4ms/SWN/src/lfo_wavetable_bank.c

// This file generated with wavecalc
// Authors: Hugo Paris, hugoplho@gmail.com, Dan Green danngreen1@gmail.com
//
// Wavetable name: 2018_08_05_HP_BetaTest_LFO_BANKS
// Wavetable by: Hugo Paris hugoplho@gmail.com

#include "arm_math.h"
#include "lfo_wavetable_bank.h"

const uint8_t lfo_sustain_pos[NUM_LFO_SHAPES] = {
	// RAMP(s) full, 3/4, 1/2,/ 18
	5,
	1,
	1,
	1,
	1,

	// REV RAMP full, 3/4, 1/2,/ 18
	243,
	192,
	128,
	64,
	32,

	// SINE, TRI, OFFSET
	133,
	134,
	128,

	// CPX SHAPES #1
	22,
	11,
	14,
	11,
	18,
	13,

	// CPX SHAPES #2
	9,
	11,
	11,
	23,
	11,
	41,
};

const uint8_t lfo_wavetable[NUM_LFO_SHAPES][LFO_TABLELEN] =
{
	// RAMP(s) full, 3/4, 1/2,/ 18

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
};
