4ms/SWN/src/sphere_flash_io.c

/*
 * sphere_flash_io.c - Spherical Wavetable Navigator I/O with external FLASH memory
 *
 * Author: Dan Green (danngreen1@gmail.com)
 *
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
 * See http://creativecommons.org/licenses/MIT/ for more information.
 *
 * -----------------------------------------------------------------------------
 */

#include "globals.h"
#include "sphere_flash_io.h"
#include "sphere.h"
#include "spheres_internal.h"

#include "drivers/flash_S25FL127.h"
#include "drivers/flashram_spidma.h"
#include "math_util.h"
#include "timekeeper.h"

#include "external_flash_layout.h"

const uint32_t 	WT_SIZE = sizeof(o_waveform)*WT_DIM_SIZE*WT_DIM_SIZE*WT_DIM_SIZE;


char	user_sphere_signature[4];
char	factory_sphere_signature[4];
char	cleared_user_sphere_signature[4];

enum SphereTypes sphere_types[MAX_TOTAL_SPHERES];

void init_sphere_flash(void)
{
	user_sphere_signature[0]='U';
	user_sphere_signature[1]='S';
	user_sphere_signature[2]='1';
	user_sphere_signature[3]='\0';

	factory_sphere_signature[0]='F';
	factory_sphere_signature[1]='S';
	factory_sphere_signature[2]='1';
	factory_sphere_signature[3]='\0';

	cleared_user_sphere_signature[0]='C';
	cleared_user_sphere_signature[1]='S';
	cleared_user_sphere_signature[2]='1';
	cleared_user_sphere_signature[3]='\0';
}

void write_factory_spheres_to_extflash(void)
{
#ifndef SKIP_FACTORY_SPHERES_IN_HEXFILE
	uint32_t wt_num;

	for (wt_num=0;wt_num<NUM_FACTORY_SPHERES;wt_num++) {
		save_sphere_to_flash(wt_num, SPHERE_TYPE_FACTORY, (int16_t *)wavetable_list[wt_num]);
	}
#endif
}
uint8_t is_wav_name(char *name) {
	uint32_t max_strlen = 31;
	uint8_t found = 0;
	while (!found && max_strlen--) {
		if (name[0]=='w' && name[1]=='a' && name[2]=='v')
			found = 1;
		if (name[0]=='s' && name[1]=='o' && name[2]=='p' && name[3]=='r')
			found = 1;
		name++;
	}
	return found;
}

void restore_factory_spheres_to_extflash(void)
{
#ifndef SKIP_FACTORY_SPHERES_IN_HEXFILE
	uint32_t wt_num;

	for (wt_num=0;wt_num<NUM_FACTORY_SPHERES;wt_num++) {
		if (read_spheretype(wt_num) != SPHERE_TYPE_FACTORY) {
			if (is_wav_name((char *)(wavetable_list[wt_num])))
				save_sphere_to_flash(wt_num, SPHERE_TYPE_FACTORY, (int16_t *)wavetable_list[wt_num]);
		}
	}
#endif
}

uint32_t get_wt_addr(uint16_t wt_num)
{
	if (wt_num >= MAX_TOTAL_SPHERES)
		wt_num = (MAX_TOTAL_SPHERES-1);

	return (sFLASH_get_sector_addr(WT_SECTOR_START + wt_num));
}	

// You must check if SPI DMA is busy before calling this or using *waveform.
// *waveform must point to a global or static memory space (not to the stack)
void load_extflash_wavetable(uint8_t wt_num, o_waveform *waveform, uint8_t x, uint8_t y, uint8_t z)
{
	uint32_t base_addr = get_wt_addr(wt_num);
	uint32_t addr;

	x = _CLAMP_U8(x,0,2);
	y = _CLAMP_U8(y,0,2);
	z = _CLAMP_U8(z,0,2);

	//calculate where the waveform is within the sphere
	addr = base_addr + sizeof(user_sphere_signature) + ((x + (y*WT_DIM_SIZE) + (z*WT_DIM_SIZE*WT_DIM_SIZE)) * SPHERE_WAVEFORM_SIZE);

	//sFLASH_read_buffer((uint8_t *)(waveform->name), addr, WT_NAME_MONITOR_CHARSIZE);

	addr += WT_NAME_MONITOR_CHARSIZE;

	sFLASH_read_buffer_DMA((uint8_t *)(waveform->wave), addr, WT_TABLELEN*BYTEDEPTH);
}

void load_extflash_wave_raw(uint8_t wt_num, int16_t *waveform, uint8_t x, uint8_t y, uint8_t z)
{
	uint32_t base_addr = get_wt_addr(wt_num);
	uint32_t addr;

	x = _CLAMP_U8(x,0,2);
	y = _CLAMP_U8(y,0,2);
	z = _CLAMP_U8(z,0,2);

	//calculate where the waveform is within the sphere
	addr = base_addr + sizeof(user_sphere_signature) + ((x + (y*WT_DIM_SIZE) + (z*WT_DIM_SIZE*WT_DIM_SIZE)) * SPHERE_WAVEFORM_SIZE);
	addr += WT_NAME_MONITOR_CHARSIZE;

	sFLASH_read_buffer_DMA((uint8_t *)waveform, addr, WT_TABLELEN*BYTEDEPTH);
}


void save_sphere_to_flash(uint8_t wt_num, enum SphereTypes sphere_type, int16_t *sphere_data){

	uint32_t sz;
	uint32_t base_addr = get_wt_addr(wt_num);

	pause_timer_IRQ(WT_INTERP_TIM_number);

	sFLASH_erase_sector(base_addr);

	//Write signature
	sz = 4;
	if (sphere_type == SPHERE_TYPE_USER)
		sFLASH_write_buffer((uint8_t *)user_sphere_signature, base_addr, sz);
	else
	if (sphere_type == SPHERE_TYPE_FACTORY)
		sFLASH_write_buffer((uint8_t *)factory_sphere_signature, base_addr, sz);
	else 
		return; //error, bad sphere_type

	base_addr += sz;

	sFLASH_write_buffer((uint8_t *)sphere_data, base_addr, WT_SIZE);

	resume_timer_IRQ(WT_INTERP_TIM_number);

	sphere_types[wt_num] = sphere_type;
}

void save_unformatted_sphere_to_flash(uint8_t wt_num, enum SphereTypes sphere_type, o_waveform sphere_data[WT_DIM_SIZE][WT_DIM_SIZE][WT_DIM_SIZE]){

	uint32_t sz;
	uint32_t base_addr = get_wt_addr(wt_num);
	uint8_t dim1 = 0;
	uint8_t dim2 = 0;
	uint8_t dim3 = 0;


	pause_timer_IRQ(WT_INTERP_TIM_number);

	sFLASH_erase_sector(base_addr);

	//Write signature
	sz = 4;
	if (sphere_type == SPHERE_TYPE_USER)
		sFLASH_write_buffer((uint8_t *)user_sphere_signature, base_addr, sz);
	else
	if (sphere_type == SPHERE_TYPE_FACTORY)
		sFLASH_write_buffer((uint8_t *)factory_sphere_signature, base_addr, sz);
	else 
		return; //error, bad sphere_type

	base_addr += sz;

	sz = sizeof(o_waveform);
	for (dim1=0; dim1<WT_DIM_SIZE; dim1++) {
		for (dim2=0; dim2<WT_DIM_SIZE; dim2++) {
			for (dim3=0; dim3<WT_DIM_SIZE; dim3++) {
				sFLASH_write_buffer((uint8_t *)(&sphere_data[dim3][dim2][dim1]), base_addr, sz);
				base_addr+=sz;
			}
		}
	}

	resume_timer_IRQ(WT_INTERP_TIM_number);

	sphere_types[wt_num] = sphere_type;
}

enum SphereTypes get_spheretype(uint32_t wt_num)
{
	return sphere_types[wt_num];
}

enum SphereTypes read_spheretype(uint32_t wt_num)
{
	uint32_t addr = get_wt_addr(wt_num);
	uint32_t sz;
	static char	read_sphere_type_data[4];

	pause_timer_IRQ(WT_INTERP_TIM_number);

	sz = 4;
	sFLASH_read_buffer((uint8_t *)read_sphere_type_data, addr, sz);

	resume_timer_IRQ(WT_INTERP_TIM_number);

	if (   read_sphere_type_data[0] == user_sphere_signature[0] 
		&& read_sphere_type_data[1] == user_sphere_signature[1] 
		&& read_sphere_type_data[2] == user_sphere_signature[2] 
		&& read_sphere_type_data[3] == user_sphere_signature[3] )
		return SPHERE_TYPE_USER;
	else
	if (   read_sphere_type_data[0] == factory_sphere_signature[0] 
		&& read_sphere_type_data[1] == factory_sphere_signature[1] 
		&& read_sphere_type_data[2] == factory_sphere_signature[2] 
		&& read_sphere_type_data[3] == factory_sphere_signature[3] )
		return SPHERE_TYPE_FACTORY;
	else
	if (   read_sphere_type_data[0] == cleared_user_sphere_signature[0] 
		&& read_sphere_type_data[1] == cleared_user_sphere_signature[1] 
		&& read_sphere_type_data[2] == cleared_user_sphere_signature[2] 
		&& read_sphere_type_data[3] == cleared_user_sphere_signature[3] )
		return SPHERE_TYPE_CLEARED;
	else
		return SPHERE_TYPE_EMPTY;

}

enum SphereTypes clear_user_sphere(uint8_t wt_num)
{
	uint32_t addr;
	uint32_t sz;
	static char	read_data[4];

	pause_timer_IRQ(WT_INTERP_TIM_number);

	sz = 4;
	addr = get_wt_addr(wt_num);
	sFLASH_read_buffer((uint8_t *)read_data, addr, sz);

	if ((sphere_types[wt_num]==SPHERE_TYPE_USER) ||
		(read_data[0] == user_sphere_signature[0] && read_data[1] == user_sphere_signature[1] && read_data[2] == user_sphere_signature[2] && read_data[3] == user_sphere_signature[3]))
	{
		sFLASH_write_buffer((uint8_t *)cleared_user_sphere_signature, addr, sz);
		sphere_types[wt_num] = SPHERE_TYPE_CLEARED;
	}
	resume_timer_IRQ(WT_INTERP_TIM_number);

	return sphere_types[wt_num];
}

enum SphereTypes unclear_user_sphere(uint8_t wt_num)
{
	uint32_t addr;
	uint32_t sz;
	static char	read_data[4];

	pause_timer_IRQ(WT_INTERP_TIM_number);

	sz = 4;
	addr = get_wt_addr(wt_num);
	sFLASH_read_buffer((uint8_t *)read_data, addr, sz);

	if ((sphere_types[wt_num]==SPHERE_TYPE_CLEARED) ||
		(read_data[0] == cleared_user_sphere_signature[0] && read_data[1] == cleared_user_sphere_signature[1] && read_data[2] == cleared_user_sphere_signature[2] && read_data[3] == cleared_user_sphere_signature[3]))
	{
		sFLASH_write_buffer((uint8_t *)user_sphere_signature, addr, sz);
		sphere_types[wt_num] = SPHERE_TYPE_USER;
	}
	resume_timer_IRQ(WT_INTERP_TIM_number);

	return sphere_types[wt_num];
}


//remove sphere signatures for user spheres
void empty_all_user_spheres(void)
{
	uint32_t addr;
	uint32_t sz;
	static char	read_data[4];
	uint8_t wt_num;

	pause_timer_IRQ(WT_INTERP_TIM_number);

	for (wt_num=0; wt_num<MAX_TOTAL_SPHERES; wt_num++)
	{
		sz = 4;
 		addr = get_wt_addr(wt_num);
 		sFLASH_read_buffer((uint8_t *)read_data, addr, sz);

		if ((sphere_types[wt_num]==SPHERE_TYPE_USER) ||
			(read_data[0] == user_sphere_signature[0] && read_data[1] == user_sphere_signature[1] && read_data[2] == user_sphere_signature[2] && read_data[3] == user_sphere_signature[3]))
		{
			read_data[0] = 0x00;
			read_data[1] = 0x00;
			read_data[2] = 0x00;
			read_data[3] = 0x00;
			sFLASH_write_buffer((uint8_t *)read_data, addr, sz);
			
			sphere_types[wt_num] = SPHERE_TYPE_EMPTY;
		}
	}
	resume_timer_IRQ(WT_INTERP_TIM_number);
}

void read_all_spheretypes(void)
{
	uint8_t i;

	for (i=0; i< MAX_TOTAL_SPHERES; i++){
		sphere_types[i] = read_spheretype(i);
	}	
}

uint8_t is_sphere_filled(uint8_t wt_num){
	if (sphere_types[wt_num] == SPHERE_TYPE_FACTORY || sphere_types[wt_num] == SPHERE_TYPE_USER) return 1;
	else return 0;
}

uint8_t all_factory_spheres_present(void){
	for (uint8_t i=0; i<NUM_FACTORY_SPHERES; i++) {
		if (read_spheretype(i)!=SPHERE_TYPE_FACTORY)
			return 0;
	}
	return 1;
}
