4ms/SWN/src/drivers/codec_sai.c

/*
 * codec_sai.c
 *
 * Author: Dan Green (danngreen1@gmail.com)
 *
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
 * See http://creativecommons.org/licenses/MIT/ for more information.
 *
 * -----------------------------------------------------------------------------
 */

#include "drivers/codec_sai.h"
#include "globals.h"
#include "hal_handlers.h"
#include "drivers/codec_i2c.h"
#include "gpio_pins.h"


//Link to the process_audio_block_codec() of the main app or the bootloader
#if IS_BOOTLOADER == 1
	#include "bootloader.h"
#else
	#include "oscillator.h"
#endif

SAI_HandleTypeDef hsai2a_rx;
SAI_HandleTypeDef hsai2b_tx;
DMA_HandleTypeDef hdma_sai2a_rx;
DMA_HandleTypeDef hdma_sai2b_tx;

DMABUFFER volatile int32_t tx_buffer[codec_BUFF_LEN];
DMABUFFER volatile int32_t rx_buffer[codec_BUFF_LEN];

enum Codec_Errors codec_dma_it_err = CODEC_NO_ERR;

uint32_t tx_buffer_start, rx_buffer_start, tx_buffer_half, rx_buffer_half;

static audio_callback_func_type audio_callback;

//Private
enum Codec_Errors init_SAI_DMA(void);
void deinit_SAI_DMA(void);
void deinit_SAI_clock(void);
void setup_SAI(uint32_t sample_rate);


void set_audio_callback(audio_callback_func_type callback)
{
	audio_callback = callback;
}

enum Codec_Errors init_SAI_clock(uint32_t sample_rate)
{
	RCC_PeriphCLKInitTypeDef PeriphClkInitStruct;
	PeriphClkInitStruct.PeriphClockSelection = RCC_PERIPHCLK_SAI2;

	//PLL input = HSE / PLLM = 16000000 / 16 = 1000000
	//PLLI2S = 1000000 * PLLI2SN / PLLI2SQ / PLLI2SDivQ

	if (sample_rate==44100)
	{
		//44.1kHz * 256 == 11 289 600
		// 		1000000 * 384 / 2 / 17
		//		= 11 294 117 = +0.04%

		PeriphClkInitStruct.PLLI2S.PLLI2SN 	= 384;	// mult by 384 = 384MHz
		PeriphClkInitStruct.PLLI2S.PLLI2SQ 	= 2;  	// div by 2 = 192MHz
		PeriphClkInitStruct.PLLI2SDivQ 		= 17; 	// div by 17 = 11.294117MHz
													// div by 256 for bit rate = 44.117kHz
	}

	else if (sample_rate==48000)
	{
		//48kHz * 256 == 12.288 MHz
		//		1000000 * 344 / 4 / 7
		//		= 12.285714MHz = -0.01%

		PeriphClkInitStruct.PLLI2S.PLLI2SN 	= 344;	// mult by 344 = 344MHz
		PeriphClkInitStruct.PLLI2S.PLLI2SQ 	= 4;  	// div by 4 = 86MHz
		PeriphClkInitStruct.PLLI2SDivQ 		= 7; 	// div by 7 = 12.285714MHz
													// div by 256 for bit rate = 47.991kHz
	}

	else if (sample_rate==96000)
	{
		//96kHz * 256 == 24.576 MHz
		//		1000000 * 344 / 2 / 7
		//		= 24.571429MHz = -0.02%
		
		PeriphClkInitStruct.PLLI2S.PLLI2SN 	= 344;	// mult by 344 = 344MHz
		PeriphClkInitStruct.PLLI2S.PLLI2SQ 	= 2;  	// div by 2 = 172MHz
		PeriphClkInitStruct.PLLI2SDivQ 		= 7; 	// div by 7 = 24.571429MHz
													// div by 256 for bit rate = 95.982kHz
	}
	else 
		return CODEC_INVALID_PARAM; //exit if sample_rate is not valid

	PeriphClkInitStruct.Sai2ClockSelection 		= RCC_SAI2CLKSOURCE_PLLI2S;
	if (HAL_RCCEx_PeriphCLKConfig(&PeriphClkInitStruct) != HAL_OK)
		return CODEC_SAI_CLK_INIT_ERR;

	return CODEC_NO_ERR;
}

enum Codec_Errors init_audio_DMA(uint32_t sample_rate)
{
	setup_SAI(sample_rate);

	tx_buffer_start = (uint32_t)&tx_buffer;
	rx_buffer_start = (uint32_t)&rx_buffer;

	tx_buffer_half = (uint32_t)(&(tx_buffer[codec_HT_LEN]));
	rx_buffer_half = (uint32_t)(&(rx_buffer[codec_HT_LEN]));

	return init_SAI_DMA();
}


void reboot_codec(uint32_t sample_rate)
{
	static uint32_t last_sample_rate;

	if (sample_rate!=44100 && sample_rate!=48000 && sample_rate!=96000)
		sample_rate = 44100;


	//Do nothing if the sample_rate did not change
	
	if (last_sample_rate != sample_rate)
	{
		last_sample_rate = sample_rate; 

		//Take everything down...
		codec_power_down();
	    codec_deinit();
	   	HAL_Delay(80);

	    deinit_SAI_clock();
	    deinit_SAI_DMA();
	   	HAL_Delay(80);

	   	//...and bring it all back up
		init_SAI_clock(sample_rate);

		codec_GPIO_init();
		init_audio_DMA(sample_rate);

		codec_I2C_init();
		codec_register_setup(sample_rate);

		start_audio();
	}

}

void start_audio(void)
{
	HAL_NVIC_EnableIRQ(CODEC_SAI_RX_DMA_IRQn); 
}

void stop_audio(void)
{
	HAL_NVIC_DisableIRQ(CODEC_SAI_RX_DMA_IRQn); 
}


void deinit_SAI_clock(void)
{
	HAL_RCCEx_DisablePLLI2S();
}

void deinit_SAI_DMA(void)
{
	HAL_NVIC_DisableIRQ(CODEC_SAI_TX_DMA_IRQn); 
	HAL_NVIC_DisableIRQ(CODEC_SAI_RX_DMA_IRQn); 

	//__HAL_RCC_DMA2_CLK_DISABLE();
	HAL_RCCEx_DisablePLLSAI();

	__HAL_RCC_SAI2_CLK_DISABLE();

	HAL_SAI_DeInit(&hsai2a_rx);
	HAL_SAI_DeInit(&hsai2b_tx);

	HAL_DMA_Abort(&hdma_sai2a_rx);
	HAL_DMA_Abort(&hdma_sai2b_tx);

	HAL_DMA_DeInit(&hdma_sai2a_rx);
	HAL_DMA_DeInit(&hdma_sai2b_tx);
}


void setup_SAI(uint32_t sample_rate)
{
	__HAL_RCC_SAI2_CLK_ENABLE();

	if (!IS_SAI_AUDIO_FREQUENCY(sample_rate)) return;

	hsai2a_rx.Instance 				= SAI2_Block_A;
	hsai2a_rx.Init.AudioMode 		= SAI_MODESLAVE_RX;
	hsai2a_rx.Init.Synchro 			= SAI_SYNCHRONOUS;
	hsai2a_rx.Init.OutputDrive 		= SAI_OUTPUTDRIVE_DISABLE;
	hsai2a_rx.Init.FIFOThreshold 	= SAI_FIFOTHRESHOLD_EMPTY;
	hsai2a_rx.Init.SynchroExt 		= SAI_SYNCEXT_DISABLE;
	hsai2a_rx.Init.MonoStereoMode 	= SAI_STEREOMODE;
	hsai2a_rx.Init.CompandingMode 	= SAI_NOCOMPANDING;
	hsai2a_rx.Init.TriState 		= SAI_OUTPUT_NOTRELEASED;

	hsai2b_tx.Instance 				= SAI2_Block_B;
	hsai2b_tx.Init.AudioMode 		= SAI_MODEMASTER_TX;
	hsai2b_tx.Init.Synchro 			= SAI_ASYNCHRONOUS;
	hsai2b_tx.Init.OutputDrive 		= SAI_OUTPUTDRIVE_DISABLE;
	hsai2b_tx.Init.NoDivider 		= SAI_MASTERDIVIDER_ENABLE;
	hsai2b_tx.Init.FIFOThreshold 	= SAI_FIFOTHRESHOLD_EMPTY;
	hsai2b_tx.Init.AudioFrequency	= sample_rate;
	hsai2b_tx.Init.SynchroExt 		= SAI_SYNCEXT_DISABLE;
	hsai2b_tx.Init.MonoStereoMode 	= SAI_STEREOMODE;
	hsai2b_tx.Init.CompandingMode 	= SAI_NOCOMPANDING;
	hsai2b_tx.Init.TriState 		= SAI_OUTPUT_NOTRELEASED;

	//
	//Don't initialize them yet, we have to de-init the DMA first
	//
	HAL_SAI_DeInit(&hsai2a_rx);
	HAL_SAI_DeInit(&hsai2b_tx);

}

enum Codec_Errors init_SAI_DMA(void)
{
	//
	// Prepare the DMA for RX (but don't enable yet)
	//
	__HAL_RCC_DMA2_CLK_ENABLE();

    hdma_sai2a_rx.Instance 					= CODEC_SAI_RX_DMA_STREAM;
    hdma_sai2a_rx.Init.Channel 				= CODEC_SAI_RX_DMA_CHANNEL;
    hdma_sai2a_rx.Init.Direction 			= DMA_PERIPH_TO_MEMORY;
    hdma_sai2a_rx.Init.PeriphInc 			= DMA_PINC_DISABLE;
    hdma_sai2a_rx.Init.MemInc 				= DMA_MINC_ENABLE;
    hdma_sai2a_rx.Init.PeriphDataAlignment 	= DMA_PDATAALIGN_WORD;
    hdma_sai2a_rx.Init.MemDataAlignment 	= DMA_MDATAALIGN_WORD;
    hdma_sai2a_rx.Init.Mode 				= DMA_CIRCULAR;
    hdma_sai2a_rx.Init.Priority 			= DMA_PRIORITY_HIGH;
    hdma_sai2a_rx.Init.FIFOMode 			= DMA_FIFOMODE_DISABLE;
	hdma_sai2a_rx.Init.MemBurst				= DMA_MBURST_SINGLE;
	hdma_sai2a_rx.Init.PeriphBurst			= DMA_PBURST_SINGLE; 

    hdma_sai2b_tx.Instance 					= CODEC_SAI_TX_DMA_STREAM;
    hdma_sai2b_tx.Init.Channel 				= CODEC_SAI_TX_DMA_CHANNEL;
    hdma_sai2b_tx.Init.Direction 			= DMA_MEMORY_TO_PERIPH;
    hdma_sai2b_tx.Init.PeriphInc 			= DMA_PINC_DISABLE;
    hdma_sai2b_tx.Init.MemInc 				= DMA_MINC_ENABLE;
    hdma_sai2b_tx.Init.PeriphDataAlignment 	= DMA_PDATAALIGN_WORD;
    hdma_sai2b_tx.Init.MemDataAlignment 	= DMA_MDATAALIGN_WORD;
    hdma_sai2b_tx.Init.Mode 				= DMA_CIRCULAR;
    hdma_sai2b_tx.Init.Priority 			= DMA_PRIORITY_HIGH;
    hdma_sai2b_tx.Init.FIFOMode 			= DMA_FIFOMODE_DISABLE;
   	hdma_sai2b_tx.Init.MemBurst				= DMA_MBURST_SINGLE;
	hdma_sai2b_tx.Init.PeriphBurst			= DMA_PBURST_SINGLE; 

	HAL_DMA_DeInit(&hdma_sai2a_rx);
	HAL_DMA_DeInit(&hdma_sai2b_tx);


	//
	// Must initialize the SAI before initializing the DMA
	//

	if (HAL_SAI_InitProtocol(&hsai2a_rx, SAI_I2S_STANDARD, SAI_PROTOCOL_DATASIZE_24BIT, 2) != HAL_OK)
		return CODEC_SAIA_INIT_ERR;

	if (HAL_SAI_InitProtocol(&hsai2b_tx, SAI_I2S_STANDARD, SAI_PROTOCOL_DATASIZE_24BIT, 2) != HAL_OK)
		return CODEC_SAIB_INIT_ERR;

	//
	// Initialize the DMA, and link to SAI
	//

    if (HAL_DMA_Init(&hdma_sai2a_rx) != HAL_OK)
     	return CODEC_SAIA_DMA_INIT_ERR;

    __HAL_LINKDMA(&hsai2a_rx,hdmarx,hdma_sai2a_rx);

	
    if (HAL_DMA_Init(&hdma_sai2b_tx) != HAL_OK)
     	return CODEC_SAIB_DMA_INIT_ERR;

    __HAL_LINKDMA(&hsai2b_tx, hdmatx, hdma_sai2b_tx);

    //
    // DMA IRQ and start DMAs
    //

	HAL_NVIC_DisableIRQ(CODEC_SAI_TX_DMA_IRQn); 
  	if (HAL_SAI_Transmit_DMA(&hsai2b_tx, (uint8_t *)tx_buffer, codec_BUFF_LEN) != HAL_OK)
  		return CODEC_SAIA_XMIT_DMA_ERR;

	HAL_NVIC_SetPriority(CODEC_SAI_RX_DMA_IRQn, 0, 0);
	HAL_NVIC_DisableIRQ(CODEC_SAI_RX_DMA_IRQn); 
	if (HAL_SAI_Receive_DMA(&hsai2a_rx, (uint8_t *)rx_buffer, codec_BUFF_LEN) != HAL_OK)
    	return CODEC_SAIB_XMIT_DMA_ERR;

	// __HAL_SAI_ENABLE(&hsai2a_rx);
	// __HAL_SAI_ENABLE(&hsai2b_tx);
	
    return CODEC_NO_ERR;
}


//DMA2_Stream2_IRQHandler
void CODEC_SAI_RX_DMA_IRQHandler(void)
{
	// HAL_DMA_IRQHandler(&hdma_sai2a_rx);
	int32_t *src, *dst;

	//Read the interrupt status register (ISR)
	uint32_t tmpisr = CODEC_SAI_RX_DMA->CODEC_SAI_RX_DMA_ISR;

	if ((tmpisr & CODEC_SAI_RX_DMA_FLAG_FE) && __HAL_DMA_GET_IT_SOURCE(&hdma_sai2a_rx, DMA_IT_FE))
		codec_dma_it_err=CODEC_DMA_IT_FE; 
		
	if ((tmpisr & CODEC_SAI_RX_DMA_FLAG_TE) && __HAL_DMA_GET_IT_SOURCE(&hdma_sai2a_rx, DMA_IT_TE))
		codec_dma_it_err=CODEC_DMA_IT_TE; 

	if ((tmpisr & CODEC_SAI_RX_DMA_FLAG_DME) && __HAL_DMA_GET_IT_SOURCE(&hdma_sai2a_rx, DMA_IT_DME))
		codec_dma_it_err=CODEC_DMA_IT_DME; 

	// Transfer Complete (TC)
	if ((tmpisr & CODEC_SAI_RX_DMA_FLAG_TC) && __HAL_DMA_GET_IT_SOURCE(&hdma_sai2a_rx, DMA_IT_TC))
	{
		// Point to 2nd half of buffers
		src = (int32_t *)(rx_buffer_half);
		dst = (int32_t *)(tx_buffer_half);

		//process_audio_block_codec(src, dst);
		audio_callback(src, dst);

		CODEC_SAI_RX_DMA->CODEC_SAI_RX_DMA_IFCR = CODEC_SAI_RX_DMA_FLAG_TC;
	}

	// Half Transfer complete (HT)
	if ((tmpisr & CODEC_SAI_RX_DMA_FLAG_HT) && __HAL_DMA_GET_IT_SOURCE(&hdma_sai2a_rx, DMA_IT_HT))
	{
		// Point to 1st half of buffers
		src = (int32_t *)(rx_buffer_start);
		dst = (int32_t *)(tx_buffer_start);

		//process_audio_block_codec(src, dst);
		audio_callback(src, dst);

		CODEC_SAI_RX_DMA->CODEC_SAI_RX_DMA_IFCR = CODEC_SAI_RX_DMA_FLAG_HT;
	}
}


// DMA2_Stream1_IRQHandler
// Does not get called, this is only here for debugging when enabling TX IRQ
// void CODEC_SAI_TX_DMA_IRQHandler(void)
// {
// 	HAL_DMA_IRQHandler(&hdma_sai2b_tx);
// }
