4ms/SWN/inc/exp_1voct_10_41V.h

/*
 * exp_1voct_10_41V.h - lookup table for 1V/oct conversion of ADC values based on a 0V to +10.41V full-scale range
 *
 * Author: Dan Green (danngreen1@gmail.com)
 *
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
 * See http://creativecommons.org/licenses/MIT/ for more information.
 *
 * -----------------------------------------------------------------------------
 */


/* 1V/octave:
 * 0V to 10.41V applied on the jack results in ADC values of 0 to 4095
 * We want to return a frequency multiplication value
 */

const float exp_1voct_10_41V[4096] = {
	1.0,
	1.00353279488337,
	1.00530386981287,
	1.00707807040643,
	1.00885540218038,
	1.01063587066072,
	1.01241948138326,
	1.01420623989355,
	1.01599615174692,
	1.01778922250853,
	1.01958545775334,
	1.02138486306616,
	1.02318744404165,
	1.02499320628435,
	1.02680215540869,
	1.02861429703901,
	1.03042963680956,
	1.03224818036455,
	1.03406993335815,
	1.03589490145451,
	1.03772309032777,
	1.03955450566208,
	1.04138915315164,
	1.04322703850067,
	1.04506816742349,
	1.04691254564448,
	1.04876017889814,
	1.05061107292908,
	1.05246523349204,
	1.05432266635193,
	1.05618337728385,
	1.05804737207305,
	1.05991465651502,
	1.06178523641547,
	1.06365911759037,
	1.06553630586592,
	1.06741680707864,
	1.06930062707533,
	1.07118777171312,
	1.07307824685945,
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
};
